pesor/TTGO-T-HIGrow/images/CaseSoilTempBottom.jpg

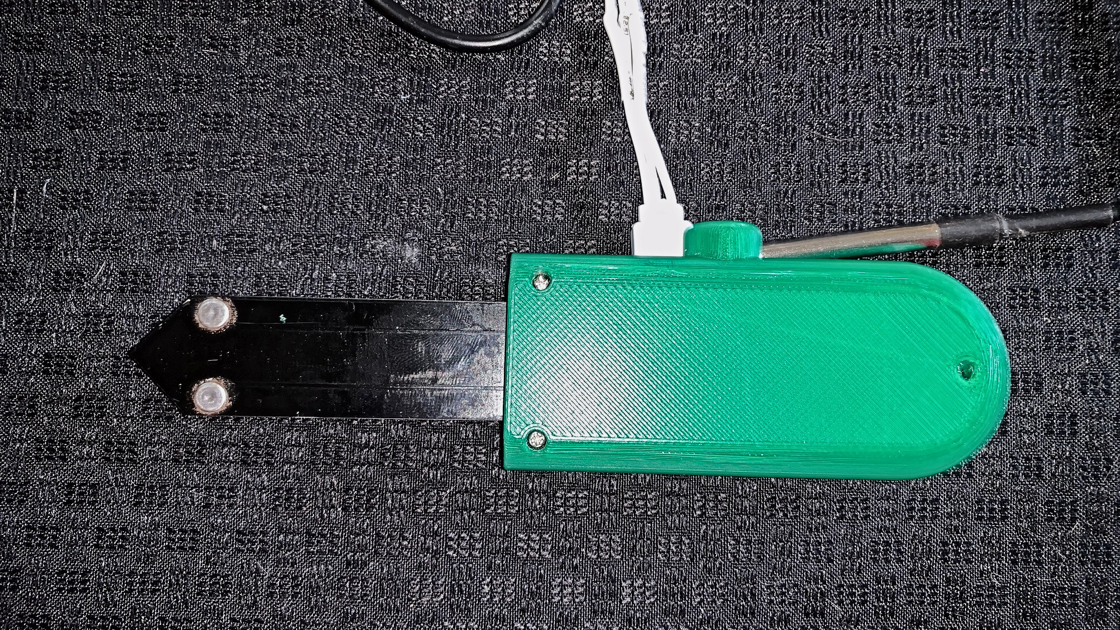
images/CaseSoilTempBottom.jpg
