pesor/TTGO-T-HIGrow/images/CaseSoilTop.jpg

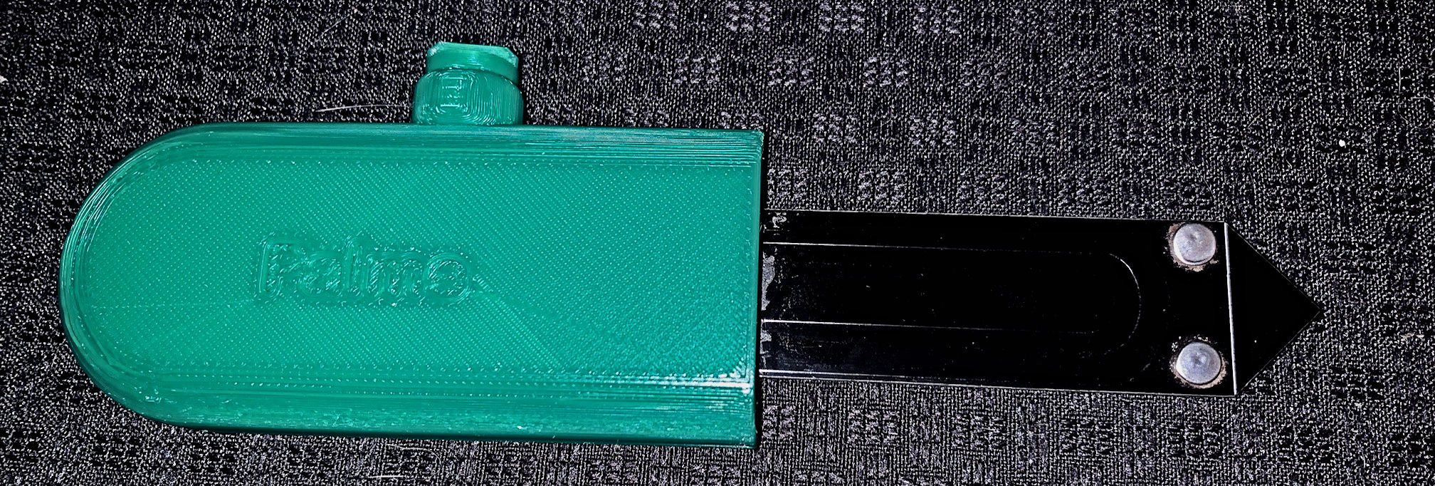
images/CaseSoilTop.jpg
