pesor/TTGO-T-HIGrow/src/time-management.h

  
  // The formattedDate comes with the following format:
  // 2018-05-28T16:00:13Z
  // We need to extract date and time
  formattedDate = timeClient.getFormattedDate();
  // Extract date
  int splitT = formattedDate.indexOf("T");
  dayStamp = formattedDate.substring(0, splitT);
  // dayStamp = dayStamp.substring(5);
  String dateYear = dayStamp.substring(0, 4 );
  String dateMonth = dayStamp.substring(5, 7);
  String dateDay = dayStamp.substring(8, 10);
  dayStamp = dateYear + "-" + dateMonth + "-" + dateDay;
  config.date = dayStamp;
  // Extract time
  // timeStamp1 = formattedDate.substring(splitT + 1, formattedDate.length() - 1);
  // config.time = timeStamp1.substring(0, 8);
  // variables needed for DST test
  int thisHour = timeClient.getHours();
  int thisDay = dateDay.toInt();
  int thisMonth = dateMonth.toInt();
  int thisWeekday = timeClient.getDay();
  bool dst = false;

  // Test for DST active
  if (thisMonth == 10 && thisDay < 25 && thisWeekday < 7 )  {
    dst = true;
  }

  if (thisMonth == 10 && thisDay > 24 && thisWeekday == 7 && thisHour < 2)  {
    dst = true;
  }

  if (thisMonth < 10 && thisMonth > 3) {
    dst = true;
  }

  if (thisMonth == 3) {
    dst = true;
    if (thisDay < 25) {
      dst = false;
    }
    else
      // thisDay > 25
    {
      if (thisWeekday == 7 && thisHour < 2)      {
        dst = false;
      }
      else {
        if (thisWeekday == 7) {
          dst = true;
        }
        else {
          if (thisWeekday < 7) {
            int checkSum = thisDay - thisWeekday + 7;
            if (checkSum > 31) {
              dst = true;
            }
            else {
              dst = false;
            }
          }
        }
      }
    }
  }

  if (dst) 
  {
    Serial.println("Czas letni");
    timeClient.setTimeOffset(gmtOffset_sec + 3600);
    while (!timeClient.update()) {
      timeClient.forceUpdate();
    }
    

  } else {
    Serial.println("czas zimowy");
  }

// The formattedDate comes with the following format:
    // 2018-05-28T16:00:13Z
    // We need to extract date and time
    formattedDate = timeClient.getFormattedDate();
    // Extract date
    // int splitT = formattedDate.indexOf("T");
    // dayStamp = formattedDate.substring(0, splitT);
    // dayStamp = dayStamp.substring(5);
    // String dateYear = dayStamp.substring(0, 4 );
    // String dateMonth = dayStamp.substring(5, 7);
    // String dateDay = dayStamp.substring(8, 10);
    // dayStamp = dateYear + "-" + dateMonth + "-" + dateDay;
    timeStamp1 = formattedDate.substring(splitT + 1, formattedDate.length() - 1);
    config.time = timeStamp1.substring(0, 8);
