pesor/TTGO-T-HIGrow/src/floatConv.h

float truncate(float val, byte dec)
{
    float x = val * pow(10, dec);
    float y = round(x);
    float z = x - y;
    if ((int)z == 5)
    {
        y++;
    } else {}
    x = y / pow(10, dec);
    return x;
}
