pesor/TTGO-T-HIGrow/src/read-batt-info.h

#include <Arduino.h>
// Read battery charging info
void read_batt_info()
{
    readFile(SPIFFS, "/batinfo.conf");
    Serial.println("Here comes the charge date info info:");
    Serial.println(readString);

    battChargeEpoc = getValue(readString, ':', 0);
    config.batchargeDate = getValue(readString, ':', 1);

    readString = "";
}
